BashithaAnthony/smart-power-quality-analyzer/media/image_2.jpeg

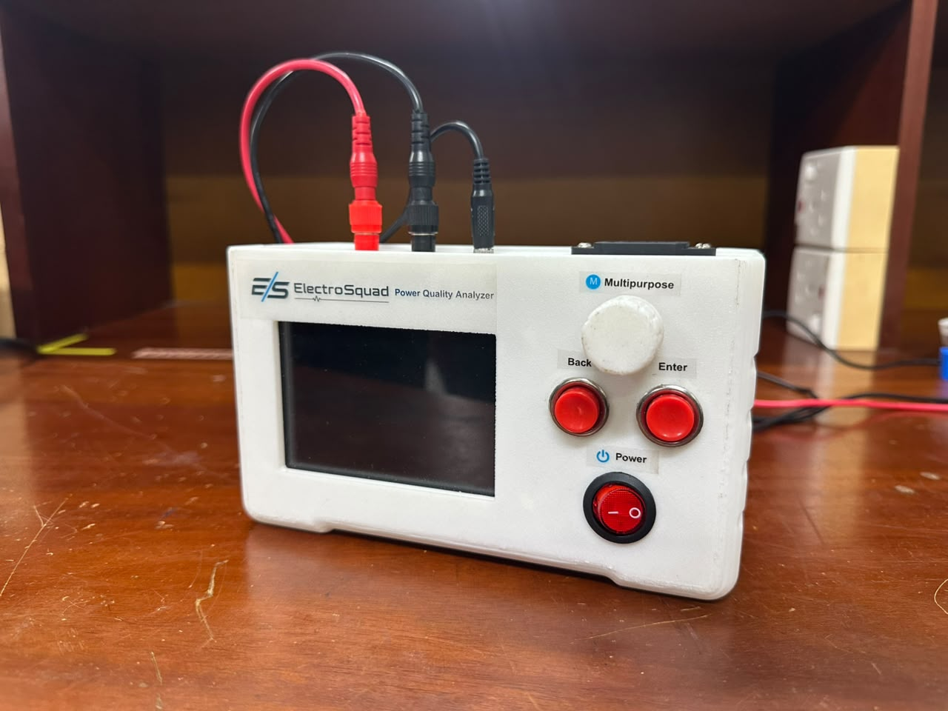
media/image_2.jpeg
