BashithaAnthony/smart-power-quality-analyzer/media/image_4.jpeg

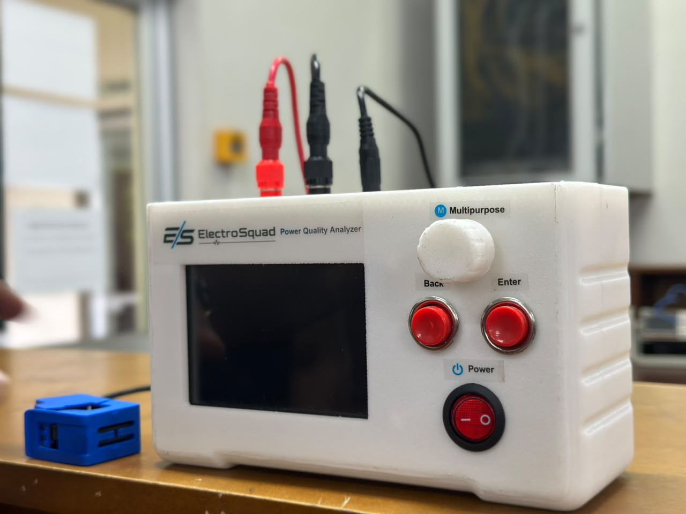
media/image_4.jpeg
