BashithaAnthony/smart-power-quality-analyzer/sketches/top.png

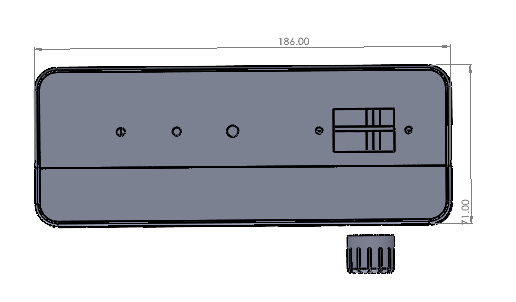
sketches/top.png
