BashithaAnthony/smart-power-quality-analyzer/embedded/ESP32_firmware/firmware/final_display/SessionStorage.h

#pragma once

#include <Arduino.h>
#include <esp_partition.h>
#include <freertos/FreeRTOS.h>
#include <freertos/semphr.h>

#include "FlashRecordCodec.h"
#include "SessionStorageFormats.h"
#include "TestConsoleConfig.h"

#ifndef SESSION_STORAGE_DEBUG
#define SESSION_STORAGE_DEBUG 0
#endif

constexpr uint32_t SESSION_STORAGE_PARTITION_BYTES = 0x00C00000U;
constexpr uint32_t SESSION_STORAGE_RESERVED_BYTES = 0x00010000U;
constexpr uint32_t SESSION_STORAGE_SEGMENT_BYTES = 0x00010000U;
constexpr uint32_t SESSION_STORAGE_SEGMENT_HEADER_BYTES =
    SESSION_SEGMENT_HEADER_BYTES;
constexpr uint32_t SESSION_STORAGE_RECORDS_PER_SEGMENT =
    SESSION_RECORDS_PER_SEGMENT;
constexpr uint32_t SESSION_STORAGE_DATA_SEGMENTS =
    SESSION_DATA_SEGMENT_COUNT;
constexpr uint32_t SESSION_STORAGE_MAX_RECORDS =
    SESSION_MAX_RETAINED_RECORDS;

static_assert(SESSION_STORAGE_RESERVED_BYTES == SESSION_STORAGE_SEGMENT_BYTES,
              "The first 64 KiB pqlog segment is reserved for metadata");
static_assert(
    (SESSION_STORAGE_PARTITION_BYTES / SESSION_STORAGE_SEGMENT_BYTES) - 1U ==
        SESSION_STORAGE_DATA_SEGMENTS,
    "pqlog must contain exactly 191 Stage 3 data segments");
static_assert(SESSION_STORAGE_SEGMENT_HEADER_BYTES +
                      SESSION_STORAGE_RECORDS_PER_SEGMENT *
                          FLASH_RECORD_BYTES ==
                  0x0000F2E0U,
              "Fourteen records must end at segment offset 0xF2E0");
static_assert(SESSION_STORAGE_SEGMENT_HEADER_BYTES +
                      (SESSION_STORAGE_RECORDS_PER_SEGMENT + 1U) *
                          FLASH_RECORD_BYTES >
                  SESSION_STORAGE_SEGMENT_BYTES,
              "A fifteenth record must not fit in a data segment");
static_assert(SESSION_STORAGE_DATA_SEGMENTS *
                      SESSION_STORAGE_RECORDS_PER_SEGMENT ==
                  SESSION_STORAGE_MAX_RECORDS,
              "Stage 3 maximum retained record count must be 2674");
static_assert(FLASH_RECORD_COMMIT_OFFSET + 4U == FLASH_RECORD_BYTES,
              "The record commit marker must be the final four bytes");
static_assert(SESSION_METADATA_COPY_B_OFFSET +
                      SESSION_METADATA_SECTOR_BYTES <=
                  SESSION_STORAGE_RESERVED_BYTES,
              "Both metadata sectors must remain in reserved pqlog space");
static_assert(SESSION_METADATA_COPY_A_OFFSET == 0U &&
                  SESSION_METADATA_COPY_B_OFFSET ==
                      SESSION_METADATA_SECTOR_BYTES,
              "Metadata copies must occupy the first two distinct sectors");
static_assert(SESSION_STORAGE_RESERVED_BYTES % 0x1000U == 0U &&
                  SESSION_STORAGE_SEGMENT_BYTES % 0x1000U == 0U,
              "Metadata and data geometry must be 4 KiB aligned");
static_assert(SESSION_METADATA_COPY_A_OFFSET % 0x1000U == 0U &&
                  SESSION_METADATA_COPY_B_OFFSET % 0x1000U == 0U &&
                  SESSION_STORAGE_SEGMENT_BYTES % 0x1000U == 0U,
              "Every erase boundary must be 4 KiB aligned");
static_assert(SESSION_STORAGE_RESERVED_BYTES +
                      SESSION_STORAGE_DATA_SEGMENTS *
                          SESSION_STORAGE_SEGMENT_BYTES ==
                  SESSION_STORAGE_PARTITION_BYTES,
              "Reserved metadata and all data segments must fill pqlog");

enum class SessionStorageError : uint8_t {
  None = 0,
  PartitionNotFound,
  AddressMismatch,
  SizeMismatch,
  EndAddressMismatch,
  EncryptedPartitionUnsupported,
  NotAvailable,
  NotPrepared,
  StoragePreparationRequired,
  StorageCapacityReached,
  RetainedSessionExists,
  NoRetainedSession,
  InvalidPersistentState,
  InvalidInterval,
  RecoveryBlocked,
  MetadataCopiesConflict,
  MetadataGenerationExhausted,
  AllocationFailed,
  NullArgument,
  BufferTooShort,
  GeometryOutOfBounds,
  LogicalIndexMismatch,
  SessionIdMismatch,
  CodecEncodeFailed,
  FlashEraseFailed,
  FlashWriteFailed,
  CommitWriteFailed,
  FlashReadFailed,
  ReadbackValidationFailed,
  RecordMetadataMismatch,
  MetadataEncodeFailed,
  MetadataValidationFailed,
  SegmentHeaderEncodeFailed,
  SegmentHeaderValidationFailed,
  RecordGapOrCorruption,
  ReaderTokenExhausted,
  ReaderAlreadyOpen,
  ReaderNotOpen,
  ReaderStale,
  ReaderEnd,
  InvalidSynchronizationTransition,
  InvalidTimeAnchor
};

struct SessionStorageStartInfo {
  uint64_t sessionId;
  uint64_t firstLogicalRecordIndex;
  uint64_t firstSegmentSequence;
};
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
