BashithaAnthony/smart-power-quality-analyzer/embedded/ESP32_firmware/firmware/final_display/AcquisitionPolicy.cpp

#include "AcquisitionPolicy.h"

#if ACQUISITION_POLICY_HOST_TEST

#include <assert.h>
#include <deque>
#include <stdio.h>
#include <vector>

namespace {

class FlushModel {
 public:
  explicit FlushModel(uint32_t capacity) : capacity_(capacity) {}

  void prepareStorage(uint32_t segmentCount) {
    assert(!accepting_);
    preparationEraseSliceCount_ =
        segmentCount * AcquisitionPolicy::eraseSlicesForSegment(65536U);
    preparationEraseYieldCount_ = preparationEraseSliceCount_;
    prepared_ = true;
  }

  void startAdmission() {
    assert(prepared_);
    accepting_ = true;
  }

  bool offer(uint32_t sequence) {
    if (!accepting_) {
      return false;
    }
    ++offered_;
    if (fifo_.size() >= capacity_) {
      ++dropped_;
      return false;
    }
    fifo_.push_back(sequence);
    ++accepted_;
    return true;
  }

  bool serviceOne(bool writeSucceeds,
                  uint32_t sequenceArrivingDuringFlash = 0U) {
    if (fifo_.empty()) {
      return false;
    }
    workerInFlight_ = true;
    if (sequenceArrivingDuringFlash != 0U) {
      offer(sequenceArrivingDuringFlash);
    }
    if (!writeSucceeds) {
      workerInFlight_ = false;
      return false;
    }
    durable_.push_back(fifo_.front());
    fifo_.pop_front();
    workerInFlight_ = false;
    ++workerYieldCount_;
    return true;
  }

  void stopAdmission() { accepting_ = false; }

  bool sequencesAreConsecutive() const {
    for (size_t index = 1U; index < durable_.size(); ++index) {
      if (durable_[index] != durable_[index - 1U] + 1U) {
        return false;
      }
    }
    return true;
  }
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
